usedgenes/Thrust-Vectoring-Rocket/Parts/Second Rod.stl

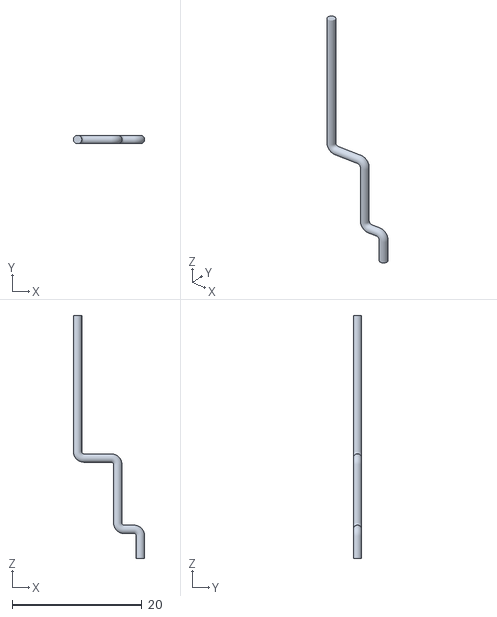
[picture p16: CAD file, 2024-07-07]
Parts/Second Rod.stl
11.0 x 1.30 x 37.5
