usedgenes/Thrust-Vectoring-Rocket/Static Fire Test Stand/IMG_2887.jpg

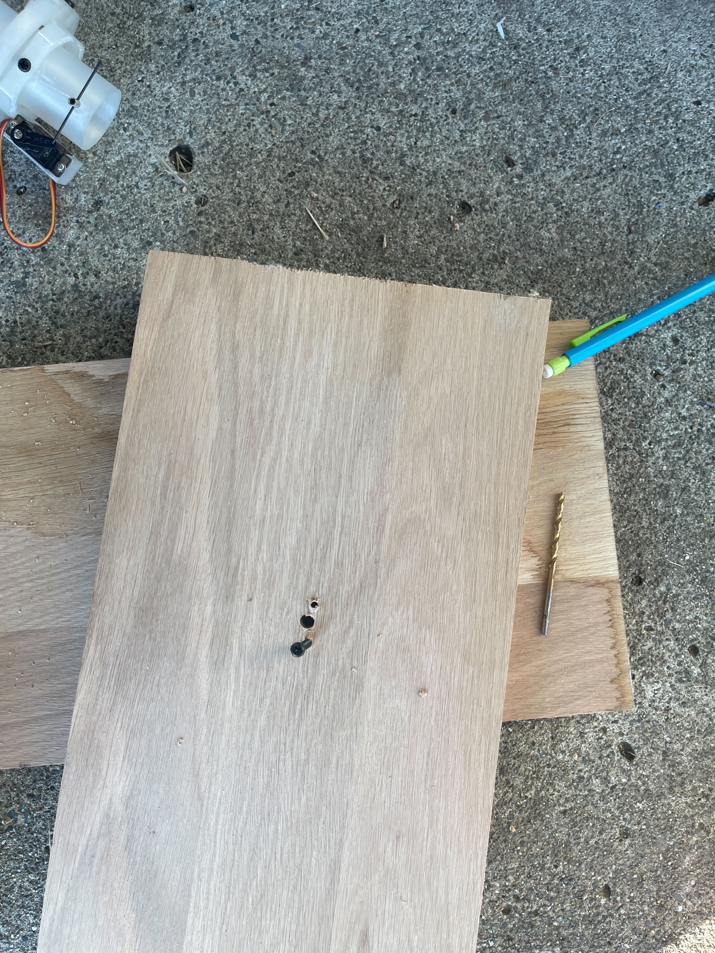
Static Fire Test Stand/IMG_2887.jpg
