usedgenes/Thrust-Vectoring-Rocket/Static Fire Test Stand/IMG_2889.jpg

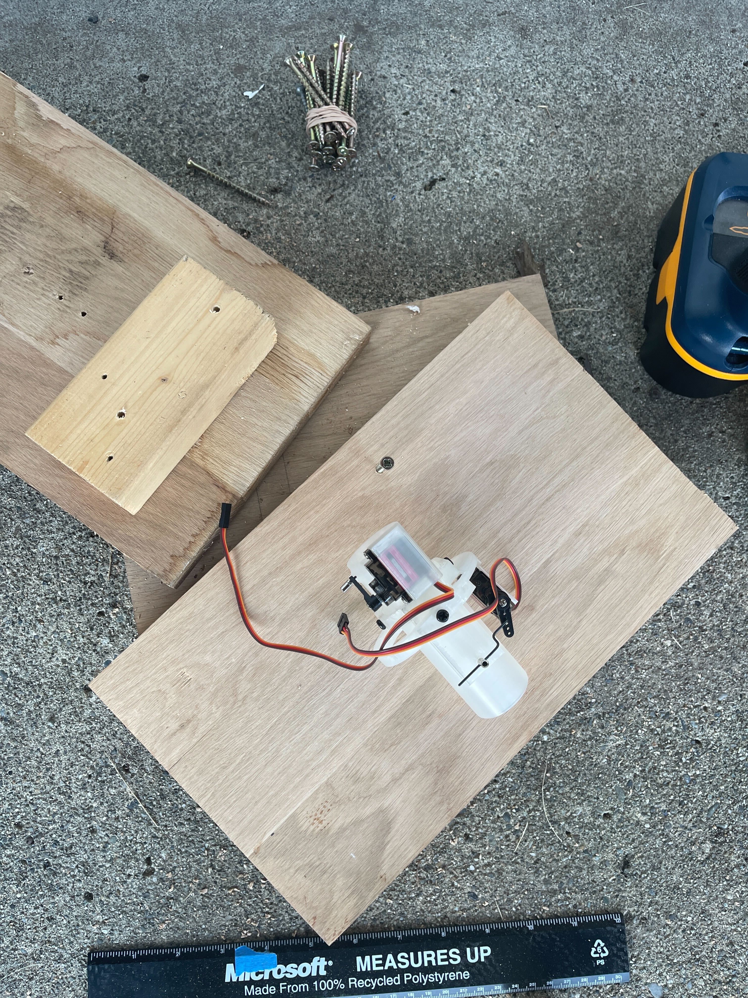
Static Fire Test Stand/IMG_2889.jpg
