usedgenes/Thrust-Vectoring-Rocket/Static Fire Test Stand/IMG_2890.jpg

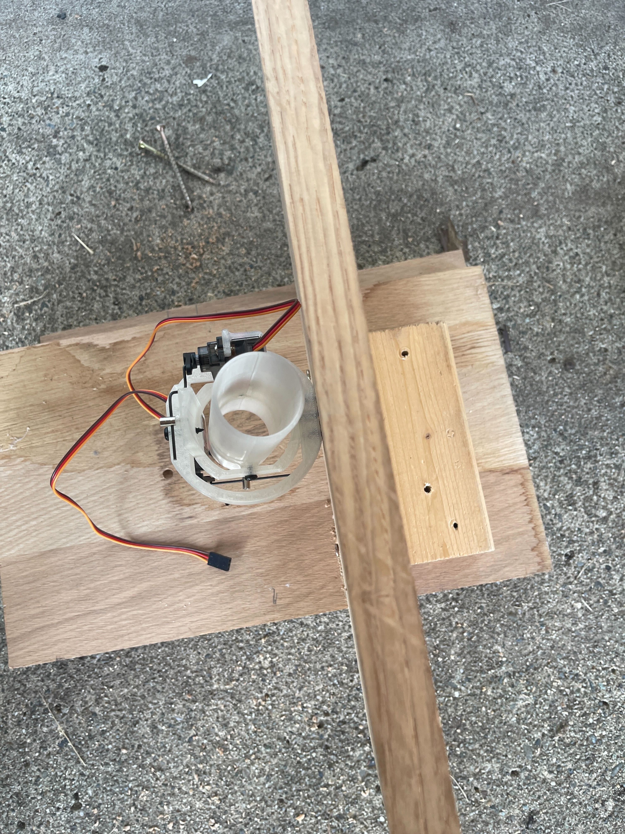
Static Fire Test Stand/IMG_2890.jpg
