usedgenes/Thrust-Vectoring-Rocket/Static Fire Test Stand/IMG_2891.jpg

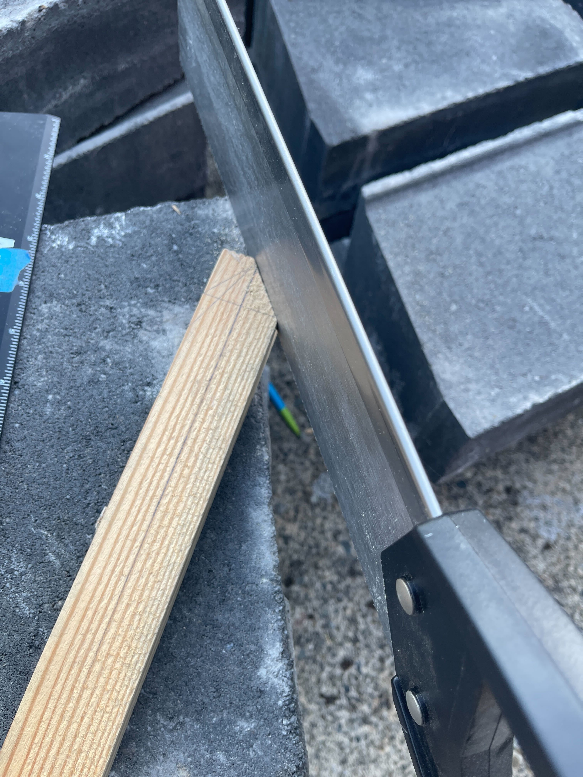
Static Fire Test Stand/IMG_2891.jpg
