usedgenes/Thrust-Vectoring-Rocket/Static Fire Test Stand/IMG_2892.jpg

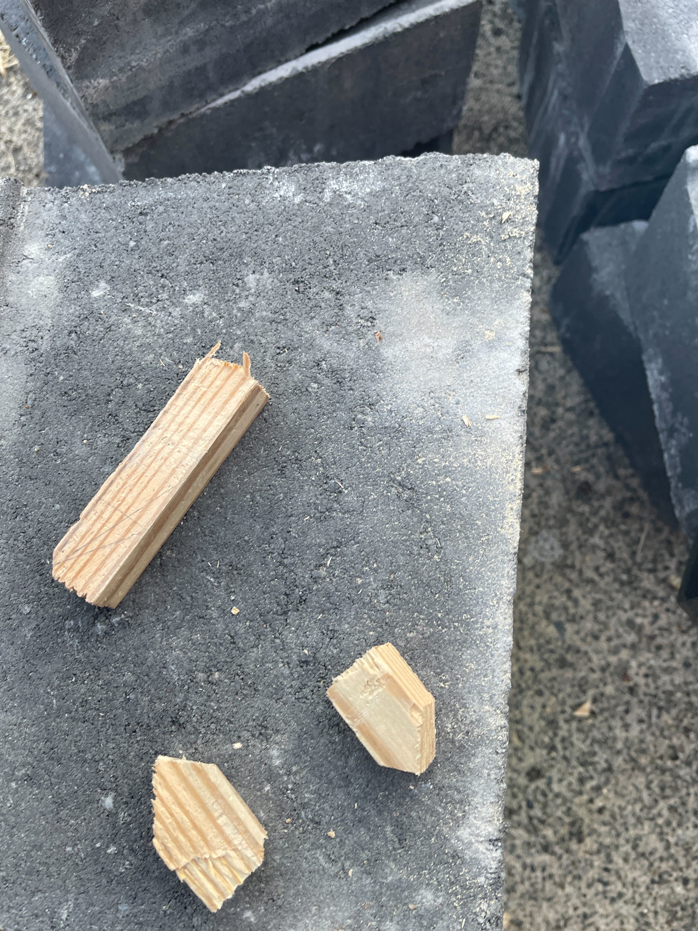
Static Fire Test Stand/IMG_2892.jpg
