usedgenes/Thrust-Vectoring-Rocket/Static Fire Test Stand/IMG_2893.jpg

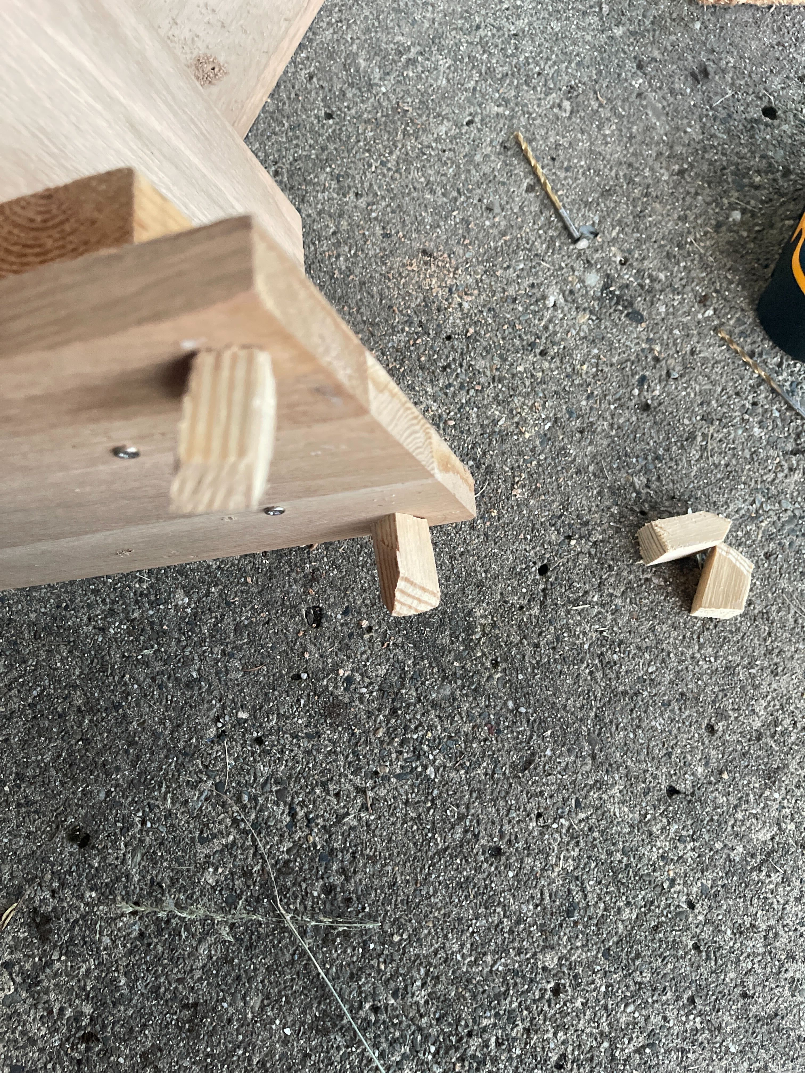
Static Fire Test Stand/IMG_2893.jpg
