usedgenes/Thrust-Vectoring-Rocket/Static Fire Test Stand/IMG_2894.jpg

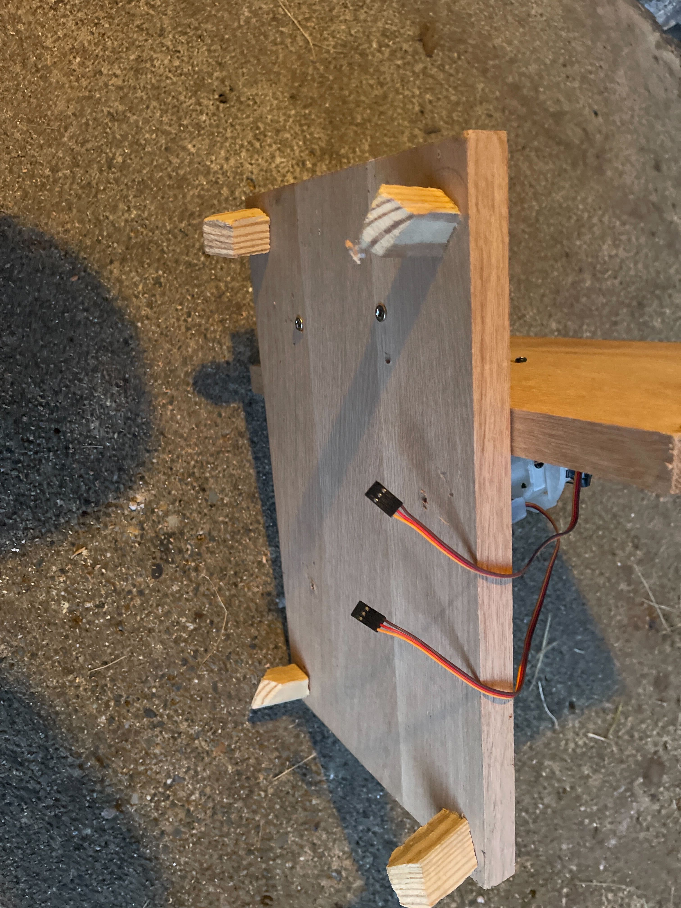
Static Fire Test Stand/IMG_2894.jpg
