usedgenes/Thrust-Vectoring-Rocket/Static Fire Test Stand/IMG_2895.jpg

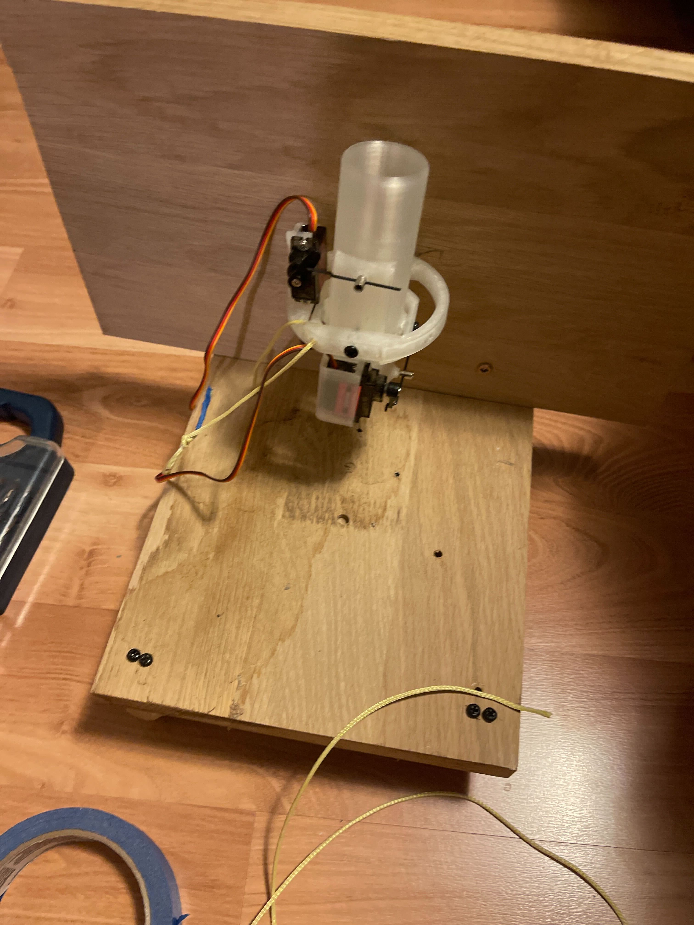
Static Fire Test Stand/IMG_2895.jpg
