usedgenes/Thrust-Vectoring-Rocket/Static Fire Test Stand/IMG_2896.jpg

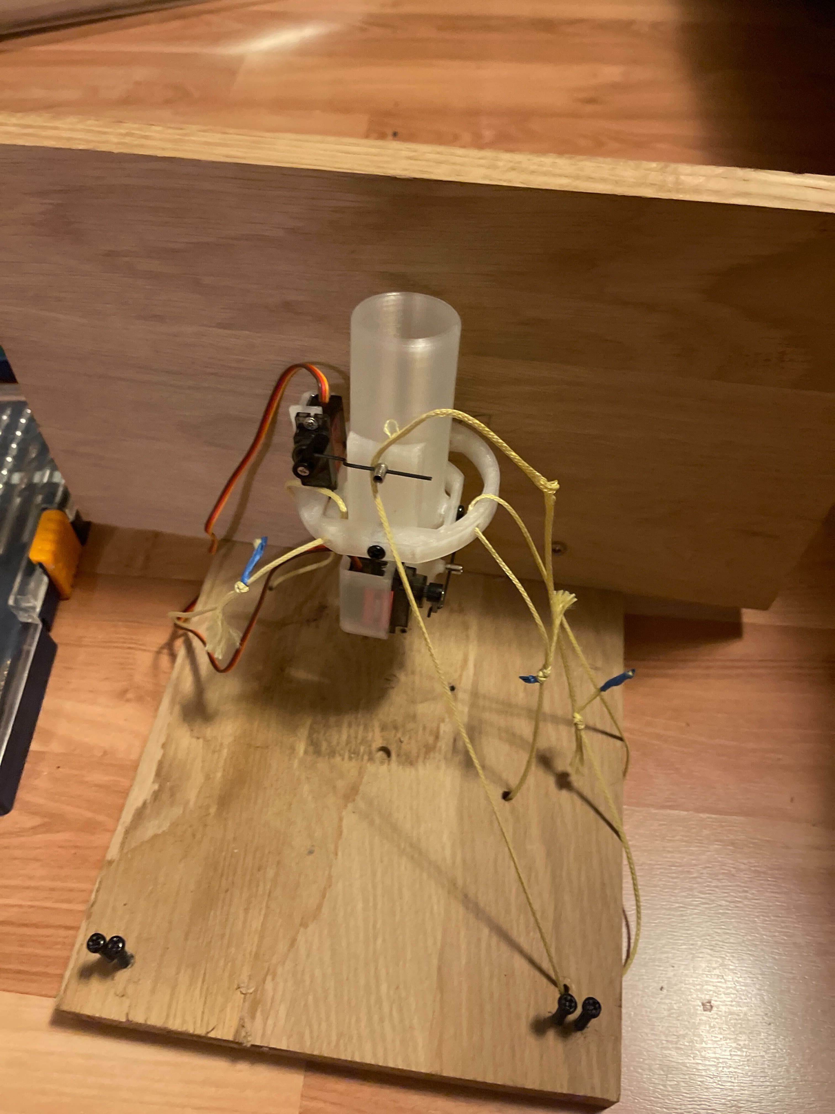
Static Fire Test Stand/IMG_2896.jpg
