usedgenes/Thrust-Vectoring-Rocket/Testing/IMG_3160.jpg

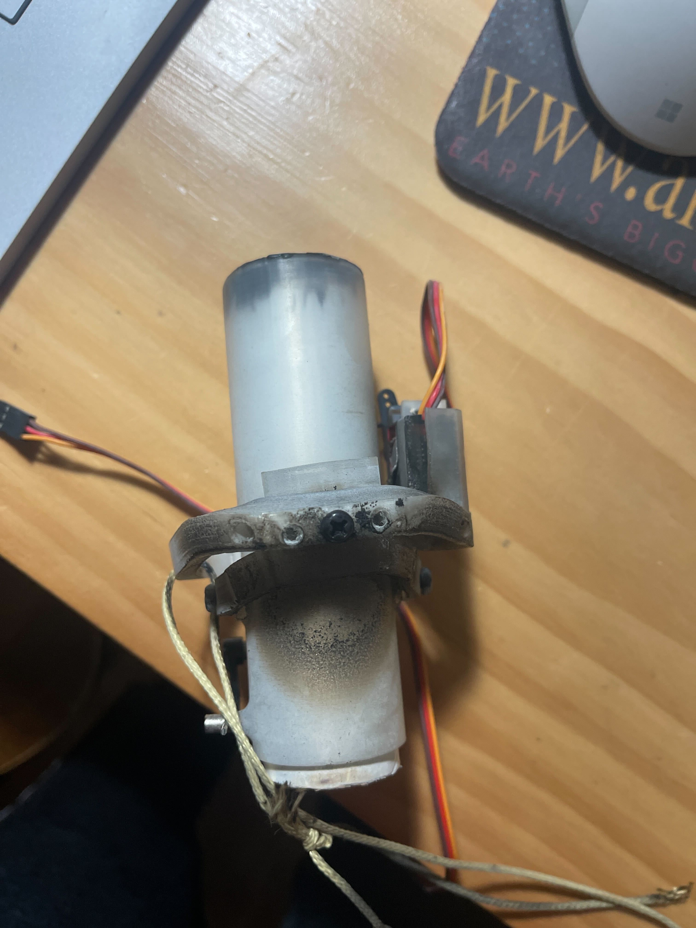
Testing/IMG_3160.jpg
