usedgenes/Thrust-Vectoring-Rocket/Testing/IMG_3163.jpg

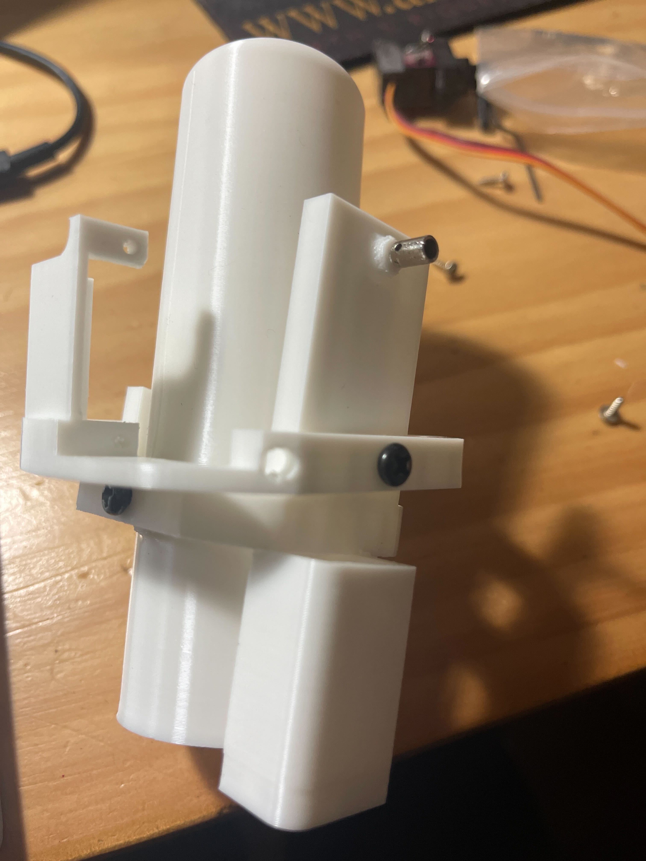
Testing/IMG_3163.jpg
