usedgenes/Thrust-Vectoring-Rocket/Arduino Code/ThrustVectoring/Utilities.h

#ifndef UTILITIES_H_
#define UTILITIES_H_

#include "Arduino.h"
#include "driver/adc.h"

class Utilities {
#define BUZZER_PIN 12
#define MAX_BATTERY_VOLTAGE 8.4
#define MIN_BATTERY_VOLTAGE 7.4
#define R1 39000  //R1 resistance (in ohms)
#define R2 68000  //R2 resistance (in ohms)
private:

public:
  //tone(pin, frequency, duration (ms))
  void Init();
  void initialized();
  float readBateryVoltageSimple();
  void readBatteryVoltage();
  void armed();
  void readApogee(int apogee);
};


#endif
